jimbaud/LAB_ObCP_L476_STM32CubeIDE/Fabrication ObCP/ORCAD_OBCP_V2_3/symbols/STEP/JST.stp

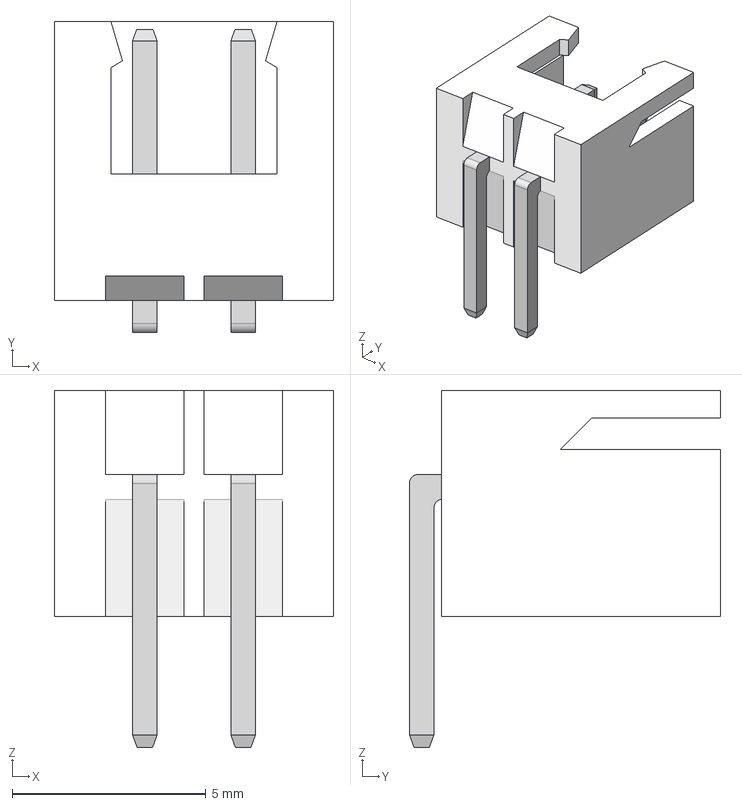
[picture p43: CAD file, 2024-11-22]
Fabrication ObCP/ORCAD_OBCP_V2_3/symbols/STEP/JST.stp
7.21 x 8.04 x 9.22 mm
