jimbaud/LAB_ObCP_L476_STM32CubeIDE/Fabrication ObCP/ORCAD_OBCP_V2_3/symbols/STEP/LITE-ON - LTST-C230KRKT.step

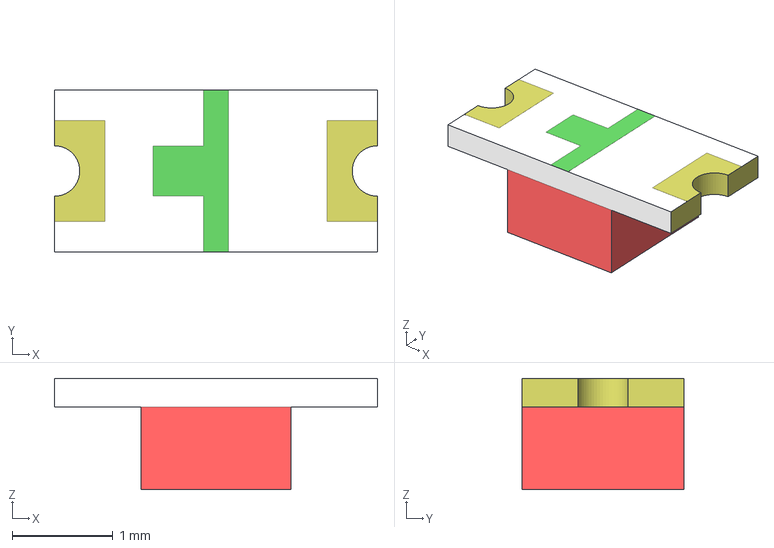
[picture p44: CAD file, 2024-11-22]
Fabrication ObCP/ORCAD_OBCP_V2_3/symbols/STEP/LITE-ON - LTST-C230KRKT.step
3.20 x 1.60 x 1.10 mm
