jimbaud/LAB_ObCP_L476_STM32CubeIDE/Fabrication ObCP/ORCAD_OBCP_V2_3/symbols/STEP/SPBTLE-RF0 v3.step

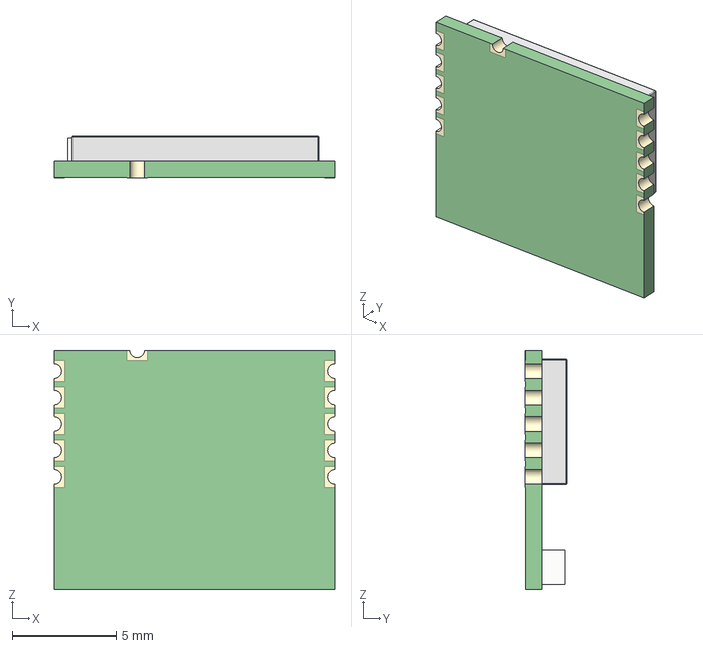
[picture p46: CAD file, 2024-11-22]
Fabrication ObCP/ORCAD_OBCP_V2_3/symbols/STEP/SPBTLE-RF0 v3.step
13.5 x 2.01 x 11.5 mm
