jimbaud/LAB_ObCP_L476_STM32CubeIDE/Fabrication ObCP/ORCAD_OBCP_V2_3/symbols/STEP/molex_0473460001.STEP

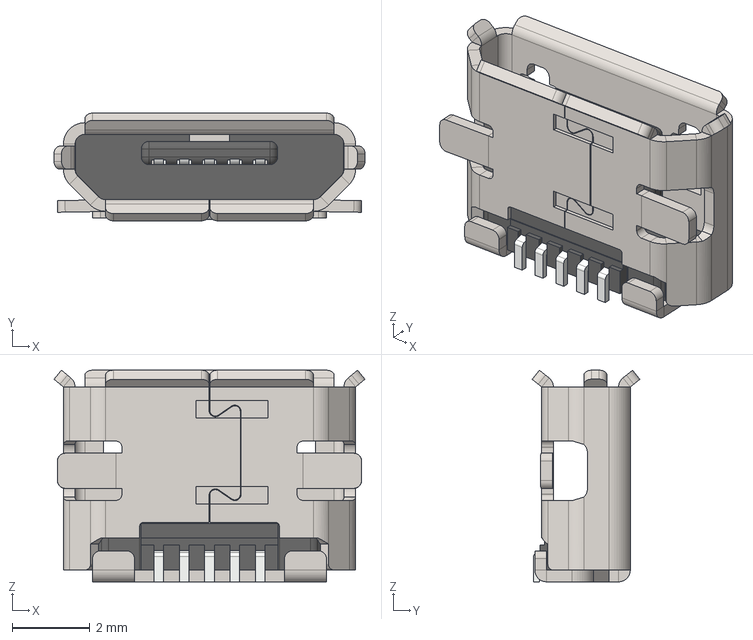
[picture p48: CAD file, 2024-11-22]
Fabrication ObCP/ORCAD_OBCP_V2_3/symbols/STEP/molex_0473460001.STEP
7.98 x 2.76 x 5.43 mm
