jimbaud/LAB_ObCP_L476_STM32CubeIDE/Fabrication ObCP/ORCAD_OBCP_V2_3/symbols/STEP/Selector Switch - MSS22D18.stp

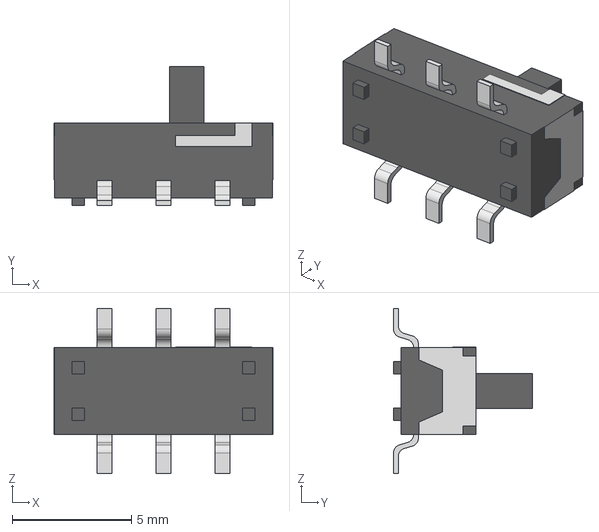
[picture p49: CAD file, 2024-11-22]
Fabrication ObCP/ORCAD_OBCP_V2_3/symbols/STEP/Selector Switch - MSS22D18.stp
9.17 x 5.82 x 6.91 mm
