jimbaud/LAB_ObCP_L476_STM32CubeIDE/Fabrication ObCP/ORCAD_OBCP_V2_3/symbols/STEP/zl201-3_p2-54_l7-62_w2-54_h8-89.stp

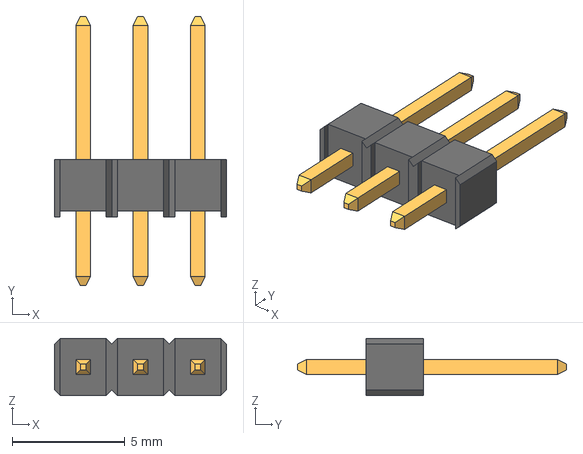
[picture p50: CAD file, 2024-11-22]
Fabrication ObCP/ORCAD_OBCP_V2_3/symbols/STEP/zl201-3_p2-54_l7-62_w2-54_h8-89.stp
7.62 x 11.9 x 2.54 mm
