jimbaud/LAB_ObCP_L476_STM32CubeIDE/Fabrication ObCP/ORCAD_OBCP_V2_3/symbols/STEP/C-0805.STEP

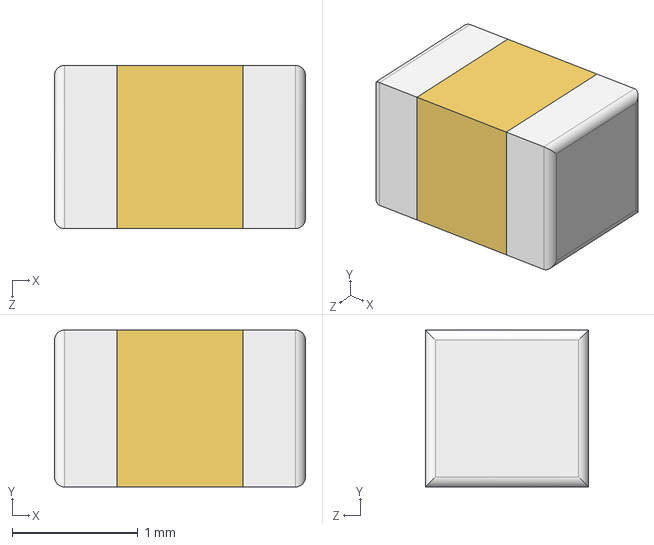
[picture p51: CAD file, 2024-11-22]
Fabrication ObCP/ORCAD_OBCP_V2_3/symbols/STEP/C-0805.STEP
2.00 x 1.25 x 1.30 mm
______1.STEP
______2.STEP x 2
