jimbaud/LAB_ObCP_L476_STM32CubeIDE/Fabrication ObCP/ORCAD_OBCP_V2_3/symbols/STEP/MO-187AA-T.stp

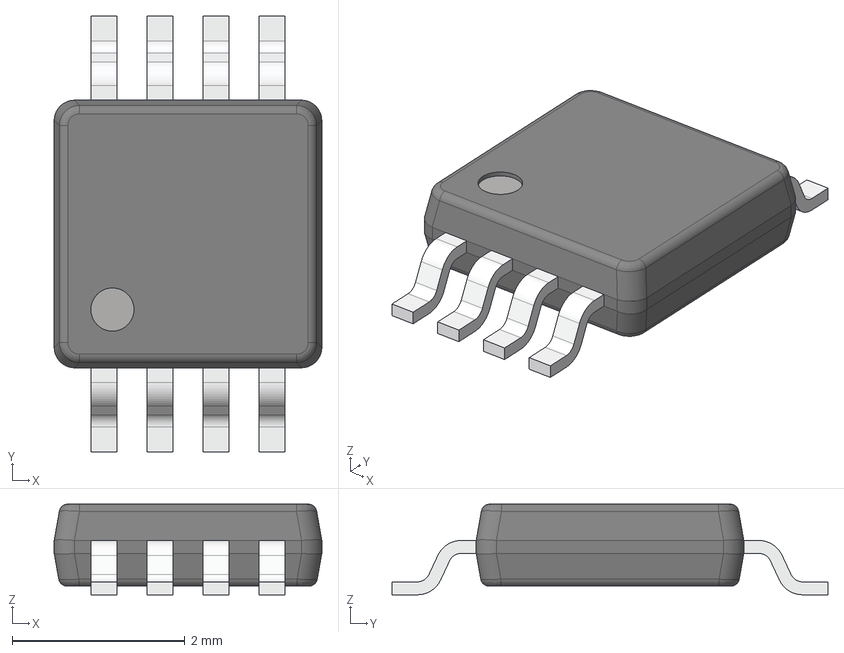
[picture p53: CAD file, 2024-11-22]
Fabrication ObCP/ORCAD_OBCP_V2_3/symbols/STEP/MO-187AA-T.stp
3.10 x 5.05 x 1.05 mm
