jimbaud/LAB_ObCP_L476_STM32CubeIDE/Fabrication ObCP/ORCAD_OBCP_V2_3/symbols/STEP/Header Socket 6-way.step

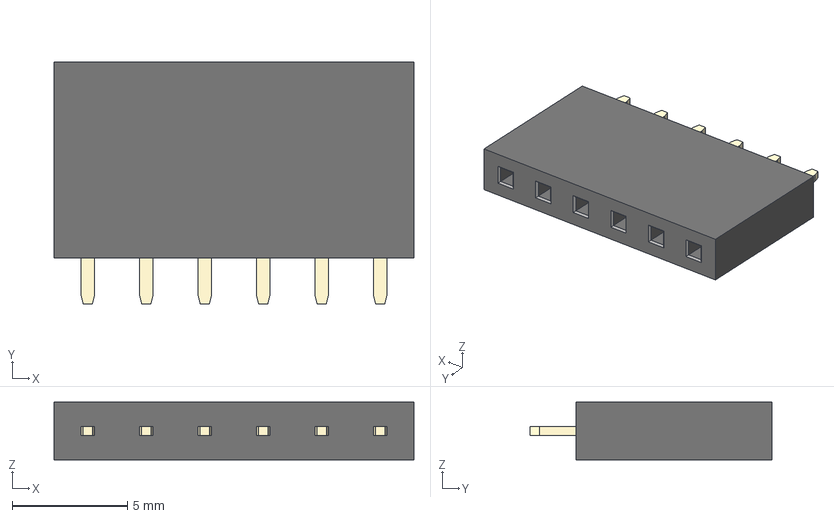
[picture p54: CAD file, 2024-11-22]
Fabrication ObCP/ORCAD_OBCP_V2_3/symbols/STEP/Header Socket 6-way.step
15.6 x 10.5 x 2.50 mm
