jimbaud/LAB_ObCP_L476_STM32CubeIDE/Fabrication ObCP/ORCAD_OBCP_V2_3/symbols/STEP/H254_90deg_3pin2.STEP

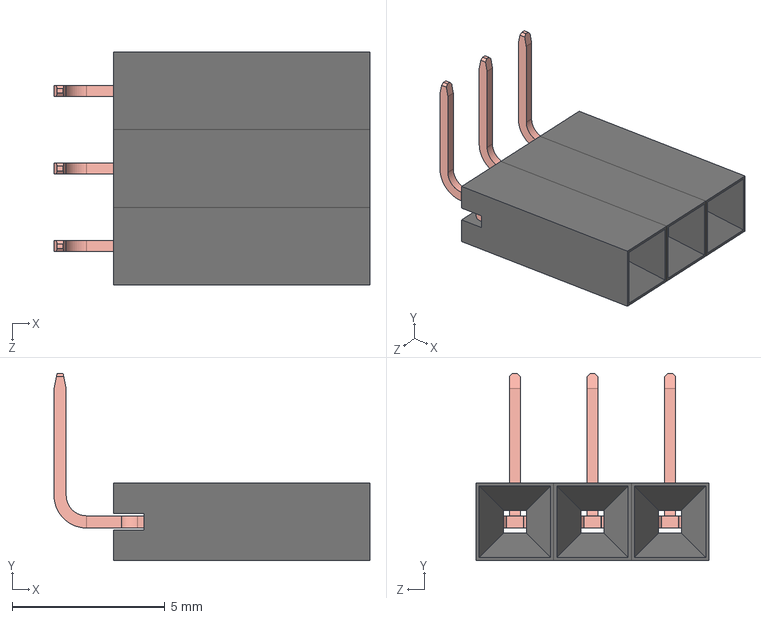
[picture p55: CAD file, 2024-11-22]
Fabrication ObCP/ORCAD_OBCP_V2_3/symbols/STEP/H254_90deg_3pin2.STEP
10.4 x 6.14 x 7.62 mm
frame_H254 x 3
pin-90deg x 3
