jimbaud/LAB_ObCP_L476_STM32CubeIDE/Fabrication ObCP/ORCAD_OBCP_V2_3/symbols/STEP/ABRACON_ABS25-32.768KHZ-6-T.STEP

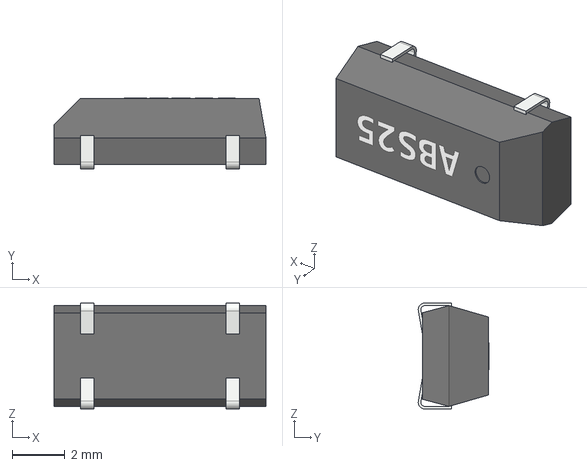
[picture p57: CAD file, 2024-11-22]
Fabrication ObCP/ORCAD_OBCP_V2_3/symbols/STEP/ABRACON_ABS25-32.768KHZ-6-T.STEP
8.00 x 2.66 x 4.00 mm
